alex-berliner/mega_blastoise/cad/renders/nintendo-faceplate.png

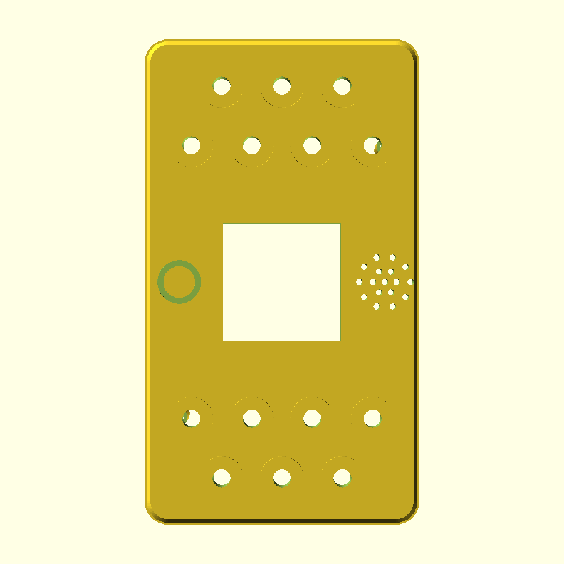
cad/renders/nintendo-faceplate.png
