alex-berliner/mega_blastoise/cad/renders/st7789-nfc-faceplate.png

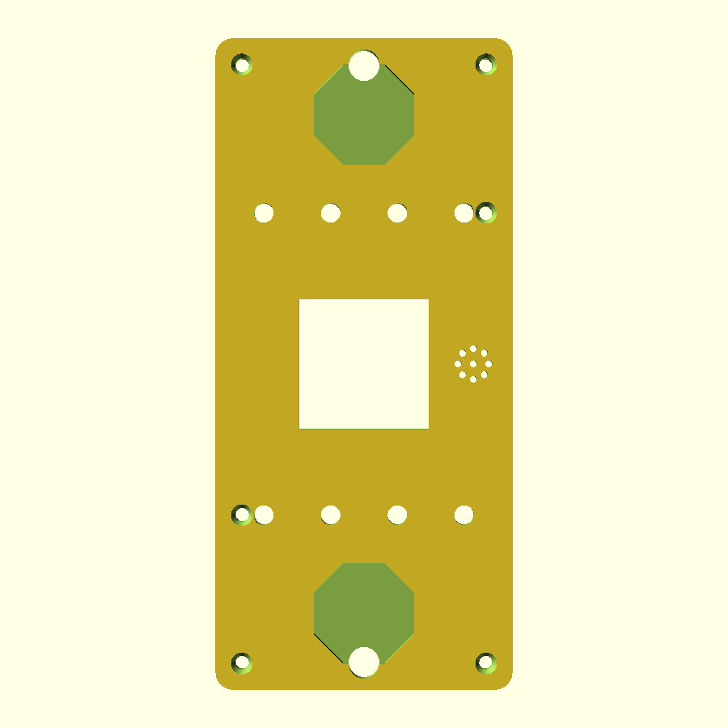
cad/renders/st7789-nfc-faceplate.png
