alex-berliner/mega_blastoise/cad/renders/variants-comparison.png

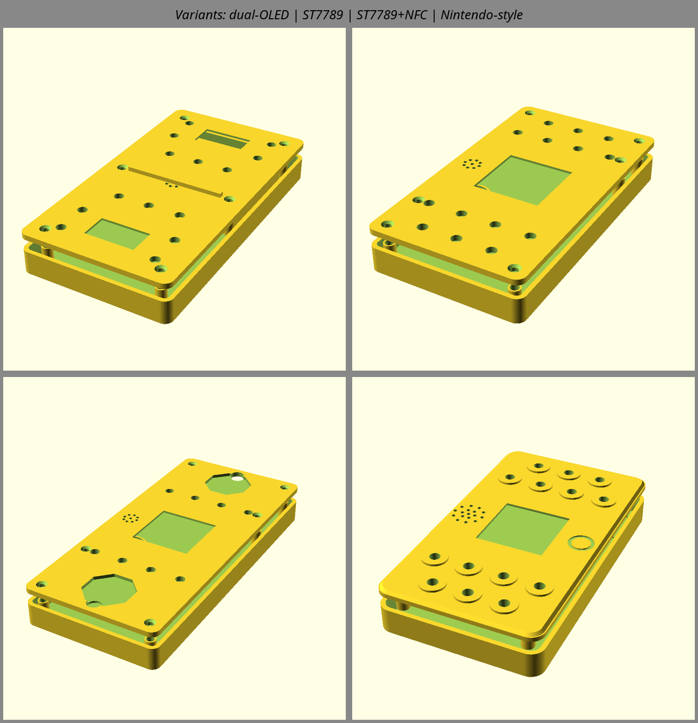
cad/renders/variants-comparison.png
