alex-berliner/mega_blastoise/mega_blastoise_fw/docs/fw_battle_turn.png

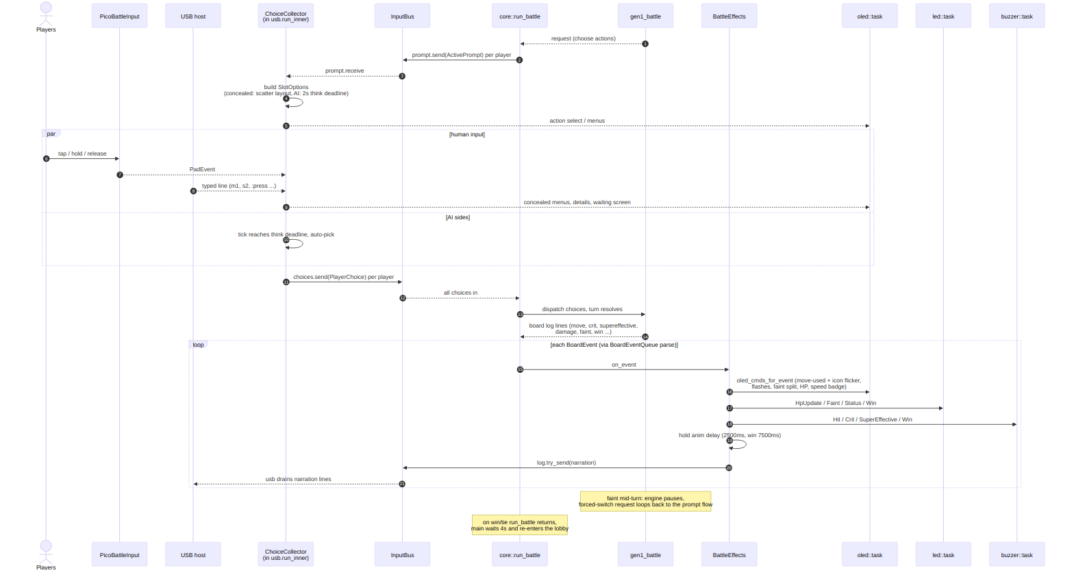
mega_blastoise_fw/docs/fw_battle_turn.png
