alex-berliner/mega_blastoise/mega_blastoise_fw/docs/fw_lobby_sequence.png

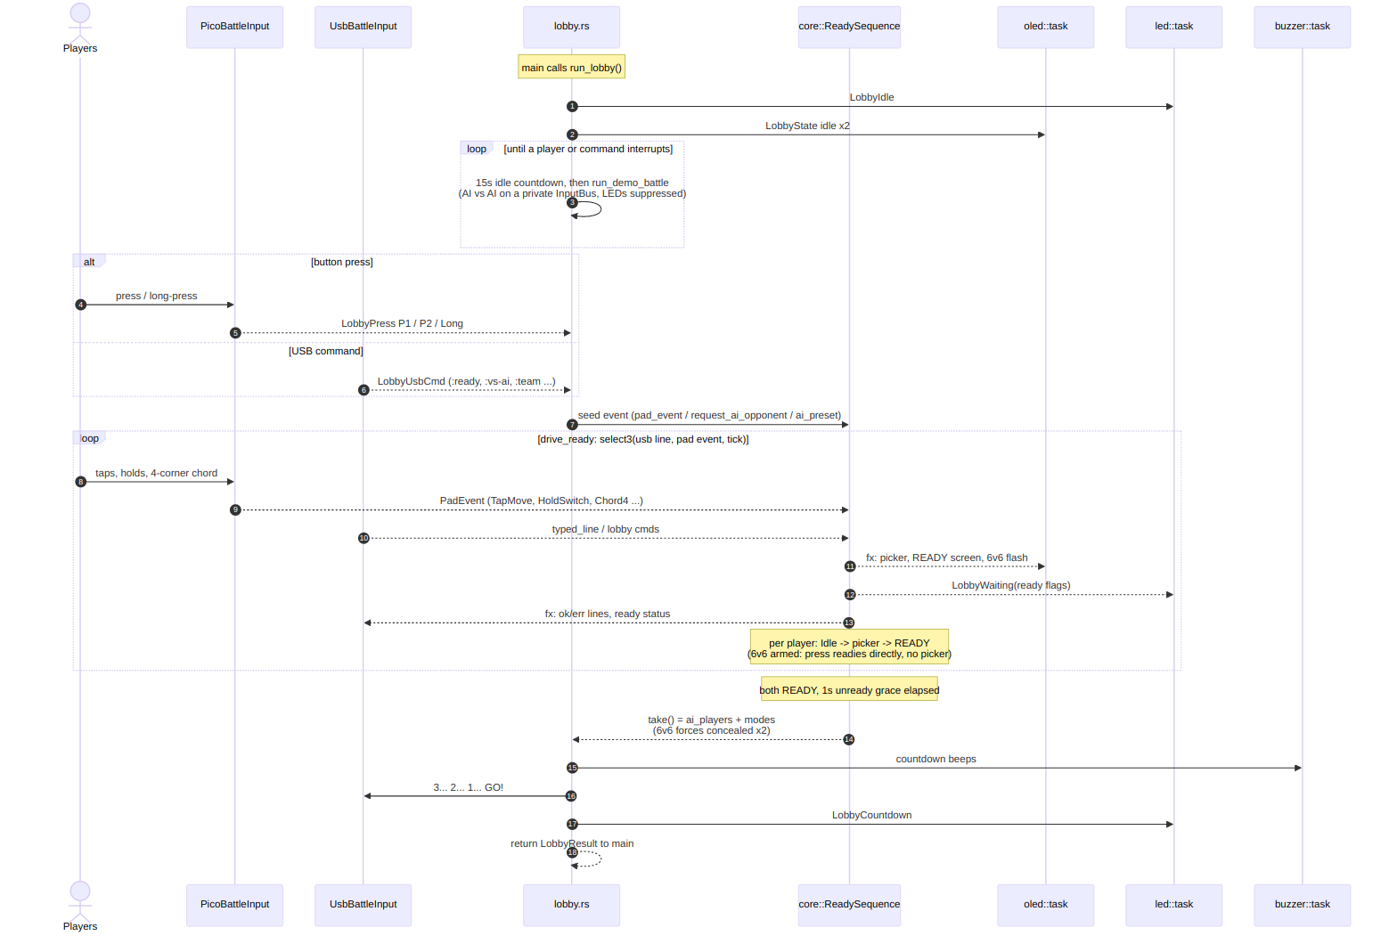
mega_blastoise_fw/docs/fw_lobby_sequence.png
