alex-berliner/mega_blastoise/mega_blastoise_fw/docs/fw_topology.png

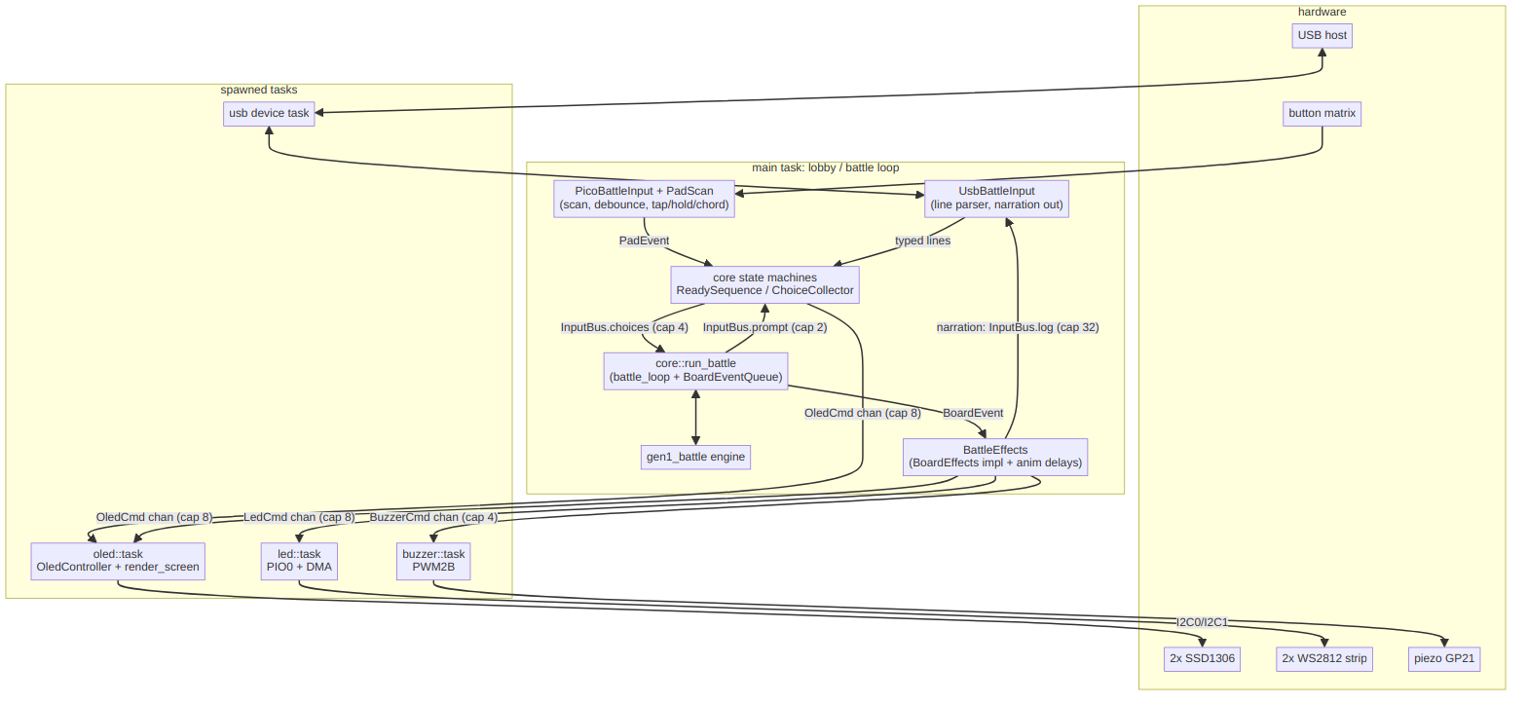
mega_blastoise_fw/docs/fw_topology.png
