alex-berliner/mega_blastoise/cad/renders/assembly-hero.png

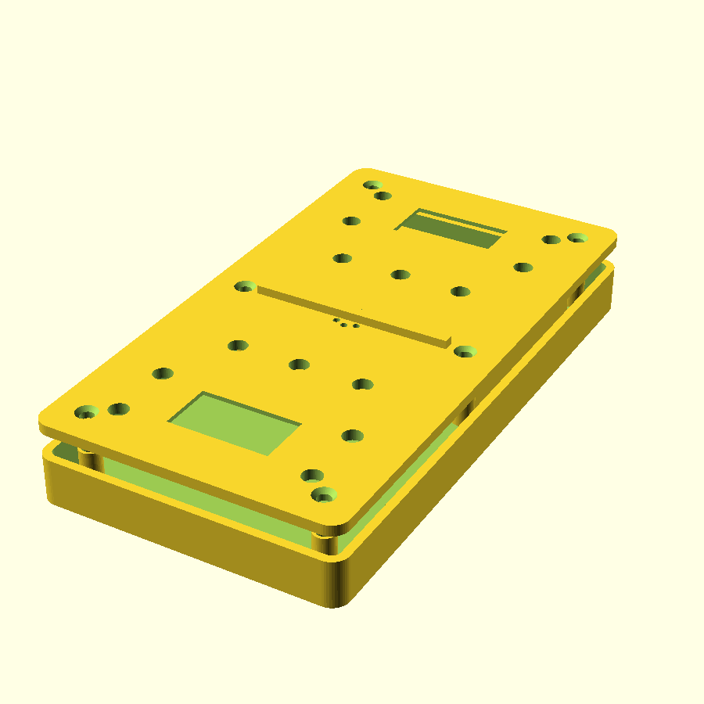
cad/renders/assembly-hero.png
