alex-berliner/mega_blastoise/cad/renders/nintendo-assembly.png

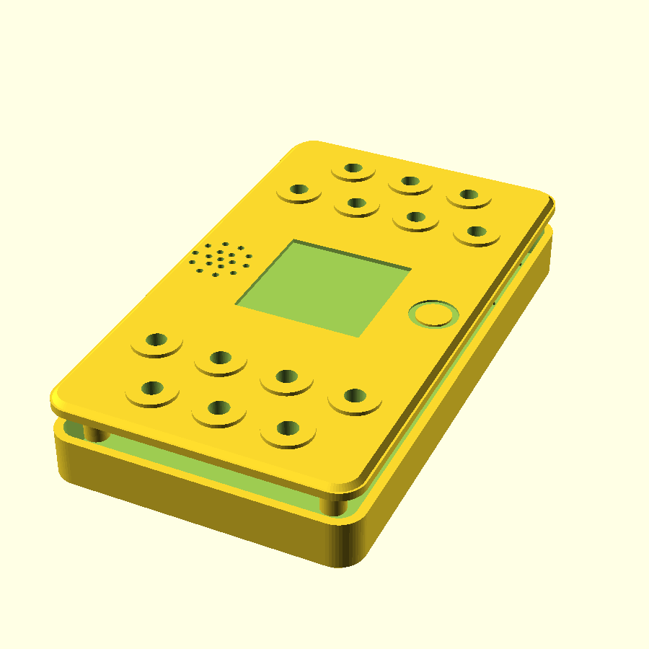
cad/renders/nintendo-assembly.png
