alex-berliner/mega_blastoise/cad/renders/st7789-assembly.png

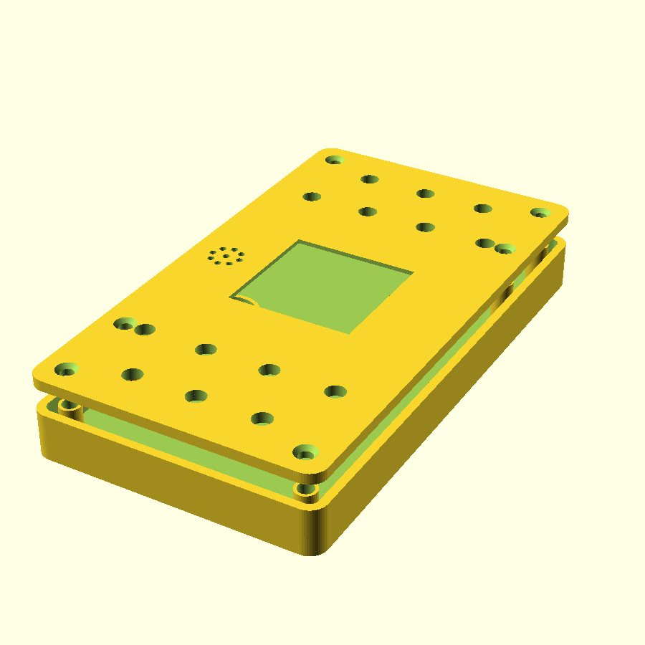
cad/renders/st7789-assembly.png
