alex-berliner/mega_blastoise/cad/renders/st7789-nfc-assembly.png

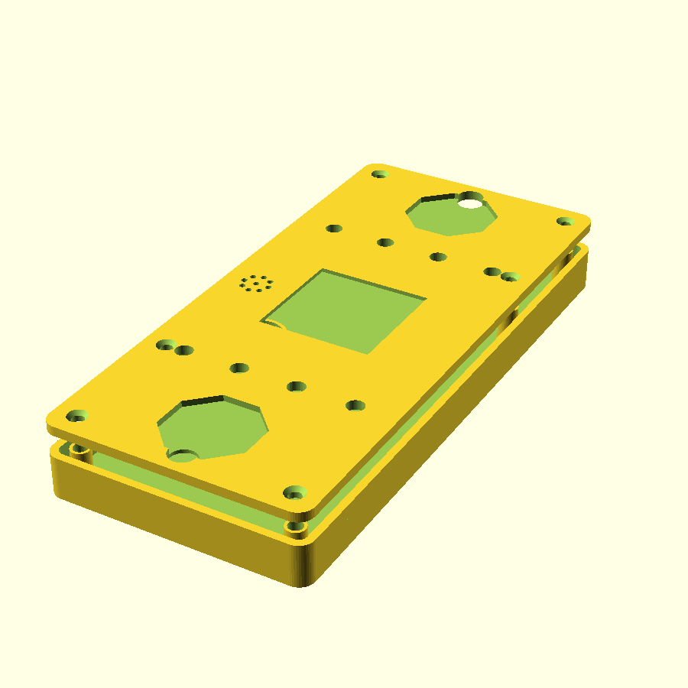
cad/renders/st7789-nfc-assembly.png
