alex-berliner/mega_blastoise/mega_blastoise_core/src/runner/gen1.rs

//! Drives a [`gen1_battle`] battle and narrates it as [`BoardEvent`]s.
//!
//! This is the Gen 1 half of the engine seam; the Gen 3 half is
//! [`crate::runner::gen3`]. Picking a ruleset picks which of the two a
//! caller drives — nothing below the [`InputBus`] knows which ran.
//!
//! The shape differs from Gen 3's because the engines differ: the battler
//! hands out `Request`s and takes choice strings back, so this runner pumps
//! that protocol, while Gen 3 steps a whole turn at once. What they share is
//! everything past the bus — both distil their seats into the neutral
//! [`crate::choice_collect::SlotOptions`], and a player cannot tell from the
//! choosing experience which engine is underneath.

extern crate alloc;

use alloc::string::ToString;

use gen1_battle::{
    BattleType, CoreBattleEngineOptions, CoreBattleOptions, FormatData, PlayerData, PlayerDex,
    PlayerOptions, PlayerType, Request, SerializedRuleSet, SideData, TeamData,
};
use battler_data::DataStore;

use core::future::Future;

use embassy_futures::select::{select, Either};

use crate::battle_effects::{BoardEffects, BoardEventQueue};
use crate::battle_input::{ActivePrompt, InputBus};
use crate::board_event::{board_prompt_event, BoardEvent, MoveSlot};

pub fn make_player(id: &str, name: &str) -> PlayerData {
    PlayerData {
        id: id.to_string(),
        name: name.to_string(),
        player_type: PlayerType::Trainer,
        player_options: PlayerOptions::default(),
        team: TeamData::default(),
        dex: PlayerDex::default(),
    }
}

pub fn battle_options_with_seed(seed: u64) -> CoreBattleOptions {
    CoreBattleOptions {
        seed: Some(seed),
        format: FormatData {
            battle_type: BattleType::Singles,
            rules: SerializedRuleSet::new(),
        },
        field: Default::default(),
        side_1: SideData {
            name: "White".to_string(),
            players: alloc::vec![make_player("p1", "White")],
        },
        side_2: SideData {
            name: "Red".to_string(),
            players: alloc::vec![make_player("p2", "Red")],
        },
    }
}

/// Idle delay (ms) at lobby start before the demo battle begins automatically.
pub const LOBBY_DEMO_DELAY_MS: u64 = 15_000;

pub fn demo_battle_options() -> CoreBattleOptions {
    CoreBattleOptions {
        seed: Some(12345),
        format: FormatData {
            battle_type: BattleType::Singles,
            rules: SerializedRuleSet::new(),
        },
        field: Default::default(),
        side_1: SideData {
            name: "White".to_string(),
            players: alloc::vec![make_player("p1", "White")],
        },
        side_2: SideData {
            name: "Red".to_string(),
            players: alloc::vec![make_player("p2", "Red")],
        },
    }
}

pub fn demo_engine_opts() -> CoreBattleEngineOptions {
    CoreBattleEngineOptions {
        validate_teams: false,
        auto_continue: true,
        reveal_actual_health: true,
        log_time: false,
        ..Default::default()
    }
}

// ── Move slot cache ───────────────────────────────────────────────────────────

// Caches per-player MoveSlot lists for the active Pokémon.  Populated once on
// SwitchIn (full CBOR decode via query_active_moves).  On subsequent Move
// events we only refresh PP from battle RAM — no CBOR decode.
struct MoveSlotCache {
    entries: alloc::vec::Vec<(alloc::string::String, alloc::vec::Vec<MoveSlot>)>,
}

impl MoveSlotCache {
    fn new() -> Self {
        Self { entries: alloc::vec::Vec::new() }
    }

    fn store(&mut self, player_id: &str, slots: alloc::vec::Vec<MoveSlot>) {
        if let Some(e) = self.entries.iter_mut().find(|(id, _)| id == player_id) {
            e.1 = slots;
        } else {
            self.entries.push((player_id.to_string(), slots));
        }
    }

    // Read current PP from battle state (no CBOR, no full PlayerBattleData), update
    // cached slots, return a clone.  Returns empty vec on cache miss.
    fn refresh_pp(
        &mut self,
        player_id: &str,
        battle: &gen1_battle::PublicCoreBattle<'_>,
    ) -> alloc::vec::Vec<MoveSlot> {
        let pp_list = battle.active_mon_move_pp(player_id).unwrap_or_default();

        let Some(entry) = self.entries.iter_mut().find(|(id, _)| id == player_id) else {
            return alloc::vec::Vec::new();
        };
        for (slot, (pp, max_pp)) in entry.1.iter_mut().zip(pp_list.iter()) {
            slot.pp = *pp;
            slot.max_pp = *max_pp;
        }
        entry.1.clone()
    }
}

// ── DataStore lookup (full CBOR decode, called only on SwitchIn) ──────────────

/// Returns (move slots, team slot index) for the currently active mon.
fn query_active_moves<DS: DataStore>(
    battle: &mut gen1_battle::PublicCoreBattle<'_>,
    data: &DS,
    player_id: &str,
) -> (alloc::vec::Vec<MoveSlot>, Option<u8>, Option<u16>) {
    let Ok(player_data) = battle.player_data(player_id) else {
        return (alloc::vec::Vec::new(), None, None);
    };
    let Some((slot_idx, active_mon)) = player_data.mons.into_iter().enumerate().find(|(_, m)| m.active) else {
        return (alloc::vec::Vec::new(), None, None);
    };
    let speed = active_mon.stats.get(&gen1_battle::Stat::Spe).copied();
    let _ = data;
    let moves = active_mon
        .moves
        .into_iter()
        .map(|mv| {
            let info = gen1_battle::move_by_id(&mv.id);
            let (power, accuracy, category) = match info {
                Some(m) => (
                    if m.power > 0 { Some(m.power as u32) } else { None },
                    if m.accuracy > 0 { Some(m.accuracy) } else { None },
                    alloc::format!("{:?}", m.category),
                ),
                None => (None, None, alloc::string::String::from("?")),
            };
            MoveSlot {
                name: mv.name,
                type_name: mv.typ.clone(),
                category,
                power,
                accuracy,
                pp: mv.pp,
                max_pp: mv.max_pp,
            }
        })
        .collect();
    (moves, Some(slot_idx as u8), speed)
}

fn query_team_slot_by_name(battle: &mut gen1_battle::PublicCoreBattle<'_>, player_id: &str, name: &str) -> Option<u8> {
    let data = battle.player_data(player_id).ok()?;
    data.mons.iter().position(|m| m.summary.name.as_str() == name).map(|i| i as u8)
}

// ── Event enrichment ──────────────────────────────────────────────────────────

async fn enrich_and_dispatch<E, DS>(
    battle: &mut gen1_battle::PublicCoreBattle<'_>,
    data: &DS,
    queue: &mut BoardEventQueue,
    effects: &mut E,
    cache: &mut MoveSlotCache,
) where
    E: BoardEffects,
    DS: DataStore,
{
    #[cfg(feature = "timing")]
    let t_drain = embassy_time::Instant::now();

    let entries: alloc::vec::Vec<alloc::string::String> =
        battle.new_log_entries().map(alloc::string::String::from).collect();
    let n_entries = entries.len();
    #[cfg(not(feature = "timing"))]
    let _ = n_entries;

    #[cfg(feature = "timing")]
    let drain_ms = t_drain.elapsed().as_millis();

    #[cfg(feature = "timing")]
    let t_parse = embassy_time::Instant::now();

    queue.push_log_lines(entries.iter().map(alloc::string::String::as_str));

    #[cfg(feature = "timing")]
    let parse_ms = t_parse.elapsed().as_millis();

    #[cfg(feature = "timing")]
    let t_enrich = embassy_time::Instant::now();

    let raw = queue.drain_pending();
    for event in raw {
        let inject = match &event {
            BoardEvent::Move { player_id: Some(pid), .. } => {
                // PP-only refresh from battle RAM — no CBOR decode.
                #[cfg(feature = "timing")]
                let t_pp = embassy_time::Instant::now();

                let moves = cache.refresh_pp(pid.as_str(), battle);

                #[cfg(feature = "timing")]
                defmt::info!("  refresh_pp({}): {}ms", pid.as_str(), t_pp.elapsed().as_millis());

                if moves.is_empty() {
                    // Cache miss (shouldn't happen after SwitchIn) — fall back.
                    #[cfg(feature = "timing")]
                    defmt::info!("  refresh_pp cache miss for {}, falling back", pid.as_str());
                    let (moves, _, _) = query_active_moves(battle, data, pid.as_str());
                    cache.store(pid.as_str(), moves.clone());
                    Some((pid.clone(), moves))
                } else {
                    Some((pid.clone(), moves))
                }
            }
            _ => None,
        };

        let mut inject_extra: Option<(alloc::string::String, alloc::vec::Vec<MoveSlot>)> = None;
        let enriched = match event {
            BoardEvent::SwitchIn { name, species, player_id, moves, .. } if moves.is_empty() => {
                // Full CBOR decode — only happens once per switch-in.
                let (new_moves, slot, speed) = player_id.as_deref().map(|pid| {
                    #[cfg(feature = "timing")]
                    let t_qam = embassy_time::Instant::now();

                    let (moves, slot, speed) = query_active_moves(battle, data, pid);
                    cache.store(pid, moves.clone());

                    #[cfg(feature = "timing")]
                    defmt::info!("  query_active_moves(SwitchIn {}): {}ms", pid, t_qam.elapsed().as_millis());

                    (moves, slot, speed)
                }).unwrap_or((alloc::vec::Vec::new(), None, None));
                BoardEvent::SwitchIn { name, species, player_id, team_slot: slot, moves: new_moves, speed }
            }
            BoardEvent::SwitchIn { name, species, player_id, moves, team_slot, speed } => {
                // Pre-populated — cache for future PP refreshes.
                if let Some(pid) = &player_id {
                    cache.store(pid.as_str(), moves.clone());
                }
                BoardEvent::SwitchIn { name, species, player_id, moves, team_slot, speed }
            }
            BoardEvent::Faint { mon, .. } => {
                let name = mon.split(',').next().unwrap_or(mon.as_str());
                let pid = mon.split(',').nth(1).unwrap_or("");
                let slot = if !pid.is_empty() { query_team_slot_by_name(battle, pid, name) } else { None };
                BoardEvent::Faint { mon, team_slot: slot }
            }
            BoardEvent::EffectStart { ref mon, ref what, .. }
                if what == "transform" || what == "mimic" =>
            {
                // The mon's move NAMES changed — the PP-only cache refresh
                // can't see that. Full re-query, refresh the cache, and
                // update the move corners.
                let pid = mon.split(',').nth(1).unwrap_or("").to_string();
                if !pid.is_empty() {
                    let (moves, _, _) = query_active_moves(battle, data, &pid);
                    cache.store(&pid, moves.clone());
                    if !moves.is_empty() {
                        inject_extra = Some((pid, moves));
                    }
                }
                event
            }
            other => other,
        };

        queue.push_event(enriched);
        if let Some((pid, moves)) = inject_extra {
            queue.push_event(BoardEvent::MovesUpdate { player_id: pid, moves });
        }
        if let Some((pid, moves)) = inject {
            queue.push_event(BoardEvent::MovesUpdate { player_id: pid, moves });
        }
    }

    #[cfg(feature = "timing")]
    let enrich_ms = t_enrich.elapsed().as_millis();

    #[cfg(feature = "timing")]
    let t_dispatch = embassy_time::Instant::now();

    queue.dispatch_all(effects).await;

    #[cfg(feature = "timing")]
    let dispatch_ms = t_dispatch.elapsed().as_millis();

    #[cfg(feature = "timing")]
    if n_entries > 0 || drain_ms + parse_ms + enrich_ms + dispatch_ms > 0 {
        defmt::info!(
            "enrich_and_dispatch: entries={} drain={}ms parse={}ms enrich={}ms dispatch={}ms",
            n_entries as u32,
            drain_ms,
            parse_ms,
            enrich_ms,
            dispatch_ms,
        );
    }
}

// ── Prompt distilling ─────────────────────────────────────────────────────────

/// Distil a Gen 1 battler request into the generation-neutral
/// [`SlotOptions`] the shared collector consumes. This is battle logic — it
/// knows the battler's `Request` shapes — which is why it lives here with the
/// Gen 1 runner and not in `choice_collect`, which must stay engine-blind.
pub fn slot_options_from_request(
    player_id: &str,
    request: &Request,
    player_data: Option<&gen1_battle::PlayerBattleData>,
) -> crate::choice_collect::SlotOptions {
    use crate::battle_input::format_move_choice;
    use crate::choice_collect::SlotOptions;
    use alloc::string::String;

    let mut s = SlotOptions::blank(
        crate::board_event::player_id_to_num(player_id),
        player_id.to_string(),
    );
    if let Some(pd) = player_data {
        for (i, ok) in s.party_ok.iter_mut().enumerate() {
            *ok = pd.mons.get(i).is_some_and(|m| !m.active && m.hp > 0);
        }
        s.party = pd.mons.iter().map(crate::display::party_slot_from_mon).collect();
    }
    match request {
        Request::Turn(turn) => {
            if let Some(mon) = turn.active.first() {
                s.active_slot = Some(mon.team_position as usize);
                let n = mon.moves.len().min(4);
                if n == 0 {
                    s.auto = Some(String::from("pass"));
                } else if mon.locked_into_move {
                    s.auto = Some(format_move_choice(0));
                } else {
                    s.n_moves = n;
                    for i in 0..n {
                        s.usable[i] = !mon.moves[i].disabled && mon.moves[i].pp > 0;
                    }
                    s.trapped = mon.trapped;
                }
            }
        }
        Request::Switch(_) => {
            s.forced_switch = true;
            // A bench of one is still the player's to send out. This used to
            // auto-commit, on the reasoning that a choice with one option is
            // not a choice — but the player is watching their last Pokemon
            // come out, and having the game make that press for them reads
            // as a dropped input rather than a courtesy. The engine
            // validates either way.
        }
        Request::TeamPreview(_) => s.auto = Some(String::from("random")),
        Request::LearnMove(_) => s.auto = Some(String::from("pass")),
    }
    s.prompt_text =
        crate::prompt_fmt::format_prompt(s.player_id.as_str(), request, player_data);
    s
}

// ── Battle runner ─────────────────────────────────────────────────────────────

pub async fn run_battle<E, T, F, DS>(
    battle: &mut gen1_battle::PublicCoreBattle<'_>,
    data: &DS,
    bus: &InputBus,
    inputs: F,
    queue: &mut BoardEventQueue,
    effects: &mut E,
    on_turn: T,
) where
    E: BoardEffects,
    T: FnMut(&mut gen1_battle::PublicCoreBattle<'_>),
    F: Future<Output = ()>,
    DS: DataStore,
{
    match select(battle_loop(battle, data, bus, queue, effects, on_turn), inputs).await {
        Either::First(()) | Either::Second(()) => {}
    }
}

async fn battle_loop<E, T, DS>(
    battle: &mut gen1_battle::PublicCoreBattle<'_>,
    data: &DS,
    bus: &InputBus,
    queue: &mut BoardEventQueue,
    effects: &mut E,
    mut on_turn: T,
) where
    E: BoardEffects,
    T: FnMut(&mut gen1_battle::PublicCoreBattle<'_>),
    DS: DataStore,
{
    let mut cache = MoveSlotCache::new();
    #[cfg(feature = "trace")]
    defmt::info!("[trace] battle_loop: start, initial dispatch");
    enrich_and_dispatch(battle, data, queue, effects, &mut cache).await;

    // The turn counter feeds only the trace logs.
    #[cfg(feature = "trace")]
    let mut turn: u32 = 0;
    while !battle.ended() {
        #[cfg(feature = "trace")]
        {
            turn += 1;
        }
        #[cfg(feature = "trace")]
        defmt::info!("[trace] battle_loop: turn {}", turn);
        let mut had_request = false;
        loop {
            // Collect ALL active requests before sending any prompts, so both
            // players are prompted simultaneously and can inspect their screens
            // in parallel without waiting on each other.
            let requests: alloc::vec::Vec<(alloc::string::String, Request)> = battle
                .active_requests()
                .map(|(pid, req)| (pid.to_string(), req.clone()))
                .collect();

            if requests.is_empty() { break; }
            had_request = true;

            #[cfg(feature = "trace")]
            defmt::info!("[trace] battle_loop: {} request(s) this turn", requests.len() as u32);

            // Send all prompts to bus.prompt before collecting any choices.
            let batch_total = requests.len();
            for (player_id, request) in &requests {
                #[cfg(feature = "trace")]
                defmt::info!("[trace] battle_loop: sending prompt to {}", player_id.as_str());
                // Refresh the OLED move corners for this prompt. Normally a
                // PP refresh from battle RAM; a recharging mon instead shows
                // its synthetic single "Recharge" option.
                if let Request::Turn(turn) = request {
                    let is_recharge = turn
                        .active
                        .first()
                        .is_some_and(|a| a.moves.len() == 1 && a.moves[0].id == "recharge");
                    let moves = if is_recharge {
                        alloc::vec![MoveSlot {
                            name: alloc::string::String::from("Recharge"),
                            type_name: alloc::string::String::from("Normal"),
                            category: alloc::string::String::from("Status"),
                            power: None,
                            accuracy: None,
                            pp: 1,
                            max_pp: 1,
                        }]
                    } else {
                        cache.refresh_pp(player_id, battle)
                    };
                    if !moves.is_empty() {
                        queue.push_event(BoardEvent::MovesUpdate {
                            player_id: player_id.clone(),
                            moves,
                        });
                    }
                }
                queue.push_event(board_prompt_event(player_id, request));
                queue.dispatch_all(effects).await;
                let player_data = battle.player_data(player_id).ok();
                let slot =
                    slot_options_from_request(player_id, request, player_data.as_ref());
                bus.prompt.send(ActivePrompt {
                    player_id: player_id.clone(),
                    slot,
                    batch_total,
                }).await;
                #[cfg(feature = "trace")]
                defmt::info!("[trace] battle_loop: prompt delivered to {}", player_id.as_str());
            }

            // Collect one choice per prompted player, routed by the id tag so
            // sources may submit in any order.
            let mut pending: alloc::vec::Vec<&str> =
                requests.iter().map(|(pid, _)| pid.as_str()).collect();
            while !pending.is_empty() {
                #[cfg(feature = "trace")]
                defmt::info!("[trace] battle_loop: waiting for {} choice(s)", pending.len() as u32);
                let submitted = bus.choices.receive().await;
                let Some(pos) = pending.iter().position(|pid| *pid == submitted.player_id) else {
                    // Duplicate or stray submission — this turn already has that
                    // player's choice (or the player has no request). Drop it.
                    #[cfg(feature = "defmt")]
                    defmt::error!(
                        "battle_loop: dropping choice for {} with no pending request",
                        submitted.player_id.as_str()
                    );
                    continue;
                };
                let player_id = pending.remove(pos);
                let line = submitted.choice;
                #[cfg(feature = "trace")]
                defmt::info!("[trace] battle_loop: got choice from {}: {}", player_id, line.as_str());

                #[cfg(feature = "timing")]
                let t0 = embassy_time::Instant::now();

                if let Err(e) = battle.set_player_choice(player_id, &line) {
                    #[cfg(feature = "defmt")]
                    defmt::error!(
                        "set_player_choice failed ({}): {}",
                        player_id,
                        defmt::Display2Format(&e.to_string())
                    );
                    #[cfg(not(feature = "defmt"))]
                    let _ = e;
                }

                #[cfg(feature = "timing")]
                defmt::info!(
                    "set_player_choice({}): {}ms",
                    player_id,
                    t0.elapsed().as_millis()
                );

                #[cfg(feature = "timing")]
                let t_ead = embassy_time::Instant::now();

                enrich_and_dispatch(battle, data, queue, effects, &mut cache).await;

                #[cfg(feature = "timing")]
                defmt::info!(
                    "enrich_and_dispatch after set_player_choice({}): {}ms",
                    player_id,
                    t_ead.elapsed().as_millis()
                );
            }
        }

        if !had_request {
            enrich_and_dispatch(battle, data, queue, effects, &mut cache).await;
            continue;
        }

        enrich_and_dispatch(battle, data, queue, effects, &mut cache).await;
        on_turn(battle);
    }
    #[cfg(feature = "trace")]
    defmt::info!("[trace] battle_loop: ended after {} turn(s)", turn);
}
