alex-berliner/mega_blastoise/mega_blastoise_web/src/lib.rs

mod web_display;
mod web_effects;

use std::cell::RefCell;
use std::collections::VecDeque;
use std::future::Future;
use std::pin::Pin;
use std::task::{Context, Poll, Waker};

use gen1_battle::TeamData;
use js_sys::Date;
use wasm_bindgen::prelude::*;
use wasm_bindgen_futures::spawn_local;

use embassy_futures::select::{select, select3, Either, Either3};
use mega_blastoise_core::{
    battle_options_with_seed, demo_engine_opts, draw_two_randbat_teams, format_active_state,
    render_screen, run_battle, ActivePrompt, BoardEventQueue,
    ChoiceCollector, CollectEffect, ControlMode, FlashDataStore, InputBus,
    OledCmd, OledController, PadEvent, PartySlotData, PlayerChoice,
    RandomAi, ReadySequence, SlotOptions,
    BATTLE_HELP, COLLECT_TICK_MS, LOBBY_DEMO_DELAY_MS,
};
use gen3_battle::Ruleset;
use mega_blastoise_core::device_session::{Button, Ctx, DeviceSession, Out};
use mega_blastoise_core::device_ui;
use web_effects::WebBattleEffects;
use web_display::WasmDisplay;

// ── Global state ──────────────────────────────────────────────────────────────

thread_local! {
    static P1_PIXELS: RefCell<Vec<u8>> = RefCell::new(vec![10, 25, 10, 255].repeat(128 * 64));
    static P2_PIXELS: RefCell<Vec<u8>> = RefCell::new(vec![10, 25, 10, 255].repeat(128 * 64));
    static LED_STATE: RefCell<[u32; 24]> = RefCell::new([0u32; 24]);

    // The single-screen device outside a battle turn: menus, options,
    // per-seat cursors and overlays, the log, and what a button means.
    // ALL of it lives in core (the fidelity rule); this cell is only where
    // the web keeps the one instance.
    static SESSION: RefCell<DeviceSession> = RefCell::new(DeviceSession::new());

    // Per-player button queues — both players can pre-queue independently
    static P1_QUEUE: RefCell<VecDeque<ButtonEvent>> = RefCell::new(VecDeque::new());
    static P1_WAKER: RefCell<Option<Waker>> = RefCell::new(None);
    static P2_QUEUE: RefCell<VecDeque<ButtonEvent>> = RefCell::new(VecDeque::new());
    static P2_WAKER: RefCell<Option<Waker>> = RefCell::new(None);

    // Battle-input queue: classified pad events and typed lines, consumed by
    // the shared ChoiceCollector loop (mirrors the firmware's USB+matrix IO).
    static BATTLE_INPUT: RefCell<VecDeque<BattleInput>> = RefCell::new(VecDeque::new());
    static BATTLE_INPUT_WAKER: RefCell<Option<Waker>> = RefCell::new(None);

    // Sticky holds (web only): a PC mouse can't hold one button while
    // clicking another, so a hold LATCHES — it stays "held down" until the
    // button is clicked again or the player commits an option. Entries are
    // (is_switch, idx), innermost last; releases are swallowed while latched.
    static HELD_LATCH: RefCell<[Vec<(bool, u8)>; 2]> = RefCell::new([Vec::new(), Vec::new()]);

    // Unlatching an OUTER button while an inner one is still latched defers
    // its HoldEnd until the inner unlatches (the screen must stay on the
    // inner view until then).
    static PENDING_END: RefCell<[u8; 2]> = RefCell::new([0; 2]);

    // Control scheme each player chose this battle (drives the web-only
    // "action buttons open instantly on click" behavior for Concealed).
    static CONTROL_MODES: RefCell<[ControlMode; 2]> = RefCell::new([ControlMode::Normal; 2]);


    // Lobby LED animation mode
    static LOBBY_MODE: RefCell<bool> = RefCell::new(false);


    // Flash events: [p1_type, p2_type]; 1 = super-effective, 2 = crit; consumed on read
    static FLASH: RefCell<[u8; 2]> = RefCell::new([0, 0]);

    // The shared two-display state machine (mega_blastoise_core::oled_ctl) —
    // identical to the firmware's. All screen decisions happen in here;
    // this file only repaints canvases when it says so. See oled_apply().
    static OLED_CTL: RefCell<OledController> = RefCell::new(OledController::new());

    // Full party snapshot per player (for AI switch picks + party LED sync;
    // the OLED controller keeps its own copy via OledCmd::PartyUpdate)
    static P1_PARTY: RefCell<Vec<PartySlotData>> = RefCell::new(Vec::new());
    static P2_PARTY: RefCell<Vec<PartySlotData>> = RefCell::new(Vec::new());

    // Which players are AI-controlled this game (reset each lobby)
    static AI_PLAYERS: RefCell<[bool; 2]> = RefCell::new([false, false]);

    // Demo mode: both AI, auto-restart each game (persists until page reload)
    static DEMO_MODE: RefCell<bool> = RefCell::new(false);

    // AI pause: when true, AI players block in wait_action/wait_switch
    static AI_PAUSED: RefCell<bool> = RefCell::new(false);

    // Pending AI config for the next game: set by VS AI button, survives the
    // loop-top reset of AI_PLAYERS, applied just before the battle starts.
    static NEXT_GAME_AI: RefCell<Option<[bool; 2]>> = RefCell::new(None);

    // When false, all animation sleeps are skipped (useful for CLI testing).
    static ANIM_ENABLED: RefCell<bool> = RefCell::new(true);

    // A button press during battle dialog skips the current animation delay
    // (consumed at the start of each delay so stale presses don't skip).
    static SKIP_DIALOG: RefCell<[bool; 2]> = RefCell::new([false, false]);

    // Screen tracer: the last [p1, p2, view] labels, so a state change logs
    // once instead of once per frame.
    static LAST_SCREEN_STATE: RefCell<[String; 3]> =
        RefCell::new([String::new(), String::new(), String::new()]);

}

// ── State accessors (pub(crate)) ──────────────────────────────────────────────

/// Apply a display command to the shared controller and repaint whichever
/// canvases it changed. The ONLY write path to the OLED canvases — mirrors
/// the firmware's OLED task loop (apply → render `ctl.screen(p)` → flush).
pub(crate) fn oled_apply(cmd: OledCmd) {
    let redraw = OLED_CTL.with(|c| c.borrow_mut().apply(cmd));
    for player in [1u8, 2] {
        if redraw.includes(player) {
            let mut disp = WasmDisplay::new();
            OLED_CTL.with(|c| render_screen(&mut disp, &c.borrow().screen(player)));
            let pixels = disp.to_rgba();
            if player == 1 { P1_PIXELS.with(|p| *p.borrow_mut() = pixels); }
            else           { P2_PIXELS.with(|p| *p.borrow_mut() = pixels); }
        }
    }
}

/// Advance the battle-screen sprite bobs — called every BOB_TICK_MS from JS,
/// mirroring the firmware's OLED-task tick. Each player's bob rate scales
/// with their active mon's Speed stat.
#[wasm_bindgen]
pub fn wasm_tick_bob() {
    let redraw = OLED_CTL.with(|c| c.borrow_mut().tick_bob(mega_blastoise_core::BOB_TICK_MS));
    for player in [1u8, 2] {
        if redraw.includes(player) {
            let mut disp = WasmDisplay::new();
            OLED_CTL.with(|c| render_screen(&mut disp, &c.borrow().screen(player)));
            let pixels = disp.to_rgba();
            if player == 1 { P1_PIXELS.with(|p| *p.borrow_mut() = pixels); }
            else           { P2_PIXELS.with(|p| *p.borrow_mut() = pixels); }
        }
    }
}

pub(crate) fn is_ai_paused() -> bool {
    AI_PAUSED.with(|p| *p.borrow())
}

pub(crate) fn is_ai_player(player: u8) -> bool {
    AI_PLAYERS.with(|a| a.borrow()[(player - 1) as usize])
}





pub(crate) fn clear_input_queues() {
    P1_QUEUE.with(|q| q.borrow_mut().clear());
    P2_QUEUE.with(|q| q.borrow_mut().clear());
}




pub(crate) fn update_leds(leds: [u32; 24]) {
    LED_STATE.with(|l| *l.borrow_mut() = leds);
}

fn status_led_color(status: Option<&str>) -> u32 {
    fn rgb(r: u8, g: u8, b: u8) -> u32 { ((r as u32) << 16) | ((g as u32) << 8) | b as u32 }
    match status {
        None | Some("") => rgb(0,   160, 0),
        Some("par")     => rgb(220, 180, 0),
        Some("brn")     => rgb(220, 20,  0),
        Some("frz")     => rgb(60,  80,  255),
        Some("psn")     => rgb(180, 60,  220),
        Some("tox")     => rgb(80,  0,   100),
        Some("slp")     => rgb(220, 80,  80),
        _               => rgb(0,   160, 0),
    }
}

/// Update HP bar (indices 0-7) for one player only.
/// Party LEDs (8-10 / 20-22) are managed separately by sync_party_leds.
pub(crate) fn update_hp_leds(player: u8, frame: [u32; 8]) {
    LED_STATE.with(|l| {
        let mut leds = l.borrow_mut();
        let base = if player == 1 { 0 } else { 12 };
        for i in 0..8 { leds[base + i] = frame[i]; }
    });
}

/// Rewrite party LEDs (3 slots per player) from P_PARTY status data.
/// Each slot is colored by status (or green if healthy, off if fainted).
/// The old dedicated status LED position (11/23) is zeroed out.
pub(crate) fn sync_party_leds(player: u8) {
    let party = if player == 1 { P1_PARTY.with(|p| p.borrow().clone()) }
                else           { P2_PARTY.with(|p| p.borrow().clone()) };
    LED_STATE.with(|l| {
        let mut leds = l.borrow_mut();
        let base = if player == 1 { 8 } else { 20 };
        let green = status_led_color(None);
        for i in 0..3usize {
            // P2's board is oriented in reverse, so mirror the slot→LED mapping.
            let party_idx = if player == 2 { 2 - i } else { i };
            leds[base + i] = if party.is_empty() {
                green // party not yet populated — default to all healthy
            } else {
                match party.get(party_idx) {
                    Some(slot) if slot.hp > 0 => status_led_color(slot.status.as_deref()),
                    _ => 0,
                }
            };
        }
        leds[base + 3] = 0; // old status-LED position — always off
    });
}

/// Patch a party slot's status in P_PARTY without a full replace.
/// Call after SetStatus/CureStatus so sync_party_leds sees the new value.
pub(crate) fn update_party_slot_status(player: u8, mon_name: &str, status: Option<String>) {
    if player == 1 {
        P1_PARTY.with(|p| {
            if let Some(slot) = p.borrow_mut().iter_mut().find(|s| s.name == mon_name) {
                slot.status = status;
            }
        });
    } else {
        P2_PARTY.with(|p| {
            if let Some(slot) = p.borrow_mut().iter_mut().find(|s| s.name == mon_name) {
                slot.status = status;
            }
        });
    }
}

/// Patch a party slot's HP in P_PARTY (used on Faint to set hp=0).
pub(crate) fn update_party_slot_hp(player: u8, mon_name: &str, hp: u16) {
    if player == 1 {
        P1_PARTY.with(|p| {
            if let Some(slot) = p.borrow_mut().iter_mut().find(|s| s.name == mon_name) {
                slot.hp = hp;
            }
        });
    } else {
        P2_PARTY.with(|p| {
            if let Some(slot) = p.borrow_mut().iter_mut().find(|s| s.name == mon_name) {
                slot.hp = hp;
            }
        });
    }
}

pub(crate) fn set_lobby_mode(active: bool) {
    LOBBY_MODE.with(|m| *m.borrow_mut() = active);
}

pub(crate) fn pack_rgb(r: u8, g: u8, b: u8) -> u32 {
    ((r as u32) << 16) | ((g as u32) << 8) | (b as u32)
}

/// Sleep unconditionally — the collector tick and countdown clocks must run
/// even with `:anim off` (sleep_ms below is animation-gated).
pub(crate) async fn sleep_ms_raw(ms: u32) {
    let promise = js_sys::Promise::new(&mut |resolve: js_sys::Function, _| {
        web_sys::window()
            .unwrap()
            .set_timeout_with_callback_and_timeout_and_arguments_0(&resolve, ms as i32)
            .unwrap();
    });
    wasm_bindgen_futures::JsFuture::from(promise).await.ok();
}

pub(crate) async fn sleep_ms(ms: u32) {
    if !ANIM_ENABLED.with(|a| *a.borrow()) { return; }
    let promise = js_sys::Promise::new(&mut |resolve: js_sys::Function, _| {
        web_sys::window()
            .unwrap()
            .set_timeout_with_callback_and_timeout_and_arguments_0(&resolve, ms as i32)
            .unwrap();
    });
    wasm_bindgen_futures::JsFuture::from(promise).await.ok();
}

/// `player` wants the current narration to move on. It only does once BOTH
/// seats have asked: a shared screen that either player can skip means one of
/// them reads half a battle. An AI seat is always willing, so a lone human
/// playing the robot still skips at their own pace.
pub(crate) fn request_dialog_skip(player: u8) {
    if (1..=2).contains(&player) {
        SKIP_DIALOG.with(|s| s.borrow_mut()[(player - 1) as usize] = true);
    }
}

fn both_want_to_skip() -> bool {
    SKIP_DIALOG.with(|s| {
        let want = s.borrow();
        (0..2).all(|i| want[i] || is_ai_player(i as u8 + 1))
    })
}

/// Animation-gated sleep that any button press cuts short (mirrors the
/// firmware's DIALOG_SKIP): polls in 50 ms slices, consuming the skip flag
/// at the start so only presses made DURING the dialog skip it.
pub(crate) async fn sleep_ms_skippable(ms: u32) {
    if !ANIM_ENABLED.with(|a| *a.borrow()) { return; }
    SKIP_DIALOG.with(|s| *s.borrow_mut() = [false, false]);
    let mut left = ms;
    while left > 0 {
        let step = left.min(50);
        sleep_ms_raw(step).await;
        if both_want_to_skip() {
            SKIP_DIALOG.with(|s| *s.borrow_mut() = [false, false]);
            return;
        }
        left -= step;
    }
}

pub(crate) fn set_flash(player: u8, flash_type: u8) {
    FLASH.with(|f| f.borrow_mut()[(player - 1) as usize] = flash_type);
}

fn lobby_led_frame() -> [u32; 24] {
    let ready = SESSION.with(|s| s.borrow().lobby_ready());
    let t = (Date::now() as u64 / 30) as u8;
    let v = (if t < 128 { t / 2 } else { (255u8.wrapping_sub(t)) / 2 }) as u32 * 2;
    // Per-player identity colors, mirroring the fw lobby: P1 white, P2 red.
    let breathe_p1 = pack_rgb(v as u8, v as u8, v as u8);
    let breathe_p2 = pack_rgb(v as u8, 0, 0);
    let done = pack_rgb(0, 200, 50);
    let mut frame = [0u32; 24];
    let c1 = if ready[0] { done } else { breathe_p1 };
    let c2 = if ready[1] { done } else { breathe_p2 };
    for i in 0..12  { frame[i] = c1; }
    for i in 12..24 { frame[i] = c2; }
    frame
}

/// `?` / `:help` — same layout as the firmware's device help; the battle
/// section is the shared BATTLE_HELP so the grammars can't drift.
fn print_help() {
    print_log("[help] Web commands");
    print_log("  Lobby:");
    for l in [
        ":ready            both players ready (human)",
        ":ready p1|p2      one player ready (human)",
        ":ready ai         P1 is AI (play as P2; also the RED VS AI button)",
        ":demo             AI vs AI demo (also the DEMO button)",
    ] {
        print_log(&format!("    {l}"));
    }
    print_log("  Any time:");
    for l in [
        ":help / :h / ?    this list",
        ":anim on|off      battle animations",
        ":screens          what each seat is looking at right now",
        ":reset            reload (new battle)",
    ] {
        print_log(&format!("    {l}"));
    }
    print_log("  In battle:");
    for l in BATTLE_HELP {
        print_log(&format!("    {l}"));
    }
}

/// Mirror a diagnostic line into the browser console, where the in-page
/// console panel picks it up. The device UI has no `#log` element, so without
/// this every event line the two-OLED page shows would vanish there.
pub(crate) fn console_log(line: &str) {
    web_sys::console::log_1(&line.into());
}

pub(crate) fn print_log(line: &str) {
    console_log(line);
    let doc = match web_sys::window().and_then(|w| w.document()) {
        Some(d) => d,
        None => return,
    };
    if let Some(el) = doc.get_element_by_id("log") {
        el.insert_adjacent_text("beforeend", &format!("{line}\n")).ok();
        el.set_scroll_top(el.scroll_height());
    }
}

// ── Button events ─────────────────────────────────────────────────────────────

pub enum ButtonEvent {
    Move   { player: u8, slot: u8 },
    Switch { player: u8, idx:  u8 },
    /// Lobby long-press: `player` wants an AI opponent.
    LongPress { player: u8 },
    /// HIDDEN: the 4-corner chord (web: all four corners tapped within 2s).
    Chord { player: u8 },
    /// A demo / VS-AI button set NEXT_GAME_AI; the lobby loop applies it.
    AiPreset,
    /// A typed lobby line for the ready sequence (picker grammar, sims).
    Line(String),
}

// Wait for either player's button (lobby start)
pub(crate) struct AnyButtonFuture;

impl Future for AnyButtonFuture {
    type Output = ButtonEvent;

    fn poll(self: Pin<&mut Self>, cx: &mut Context<'_>) -> Poll<ButtonEvent> {
        let ev = P1_QUEUE.with(|q| q.borrow_mut().pop_front())
            .or_else(|| P2_QUEUE.with(|q| q.borrow_mut().pop_front()));
        if let Some(ev) = ev {
            Poll::Ready(ev)
        } else {
            P1_WAKER.with(|w| *w.borrow_mut() = Some(cx.waker().clone()));
            P2_WAKER.with(|w| *w.borrow_mut() = Some(cx.waker().clone()));
            Poll::Pending
        }
    }
}

// Wait for a specific player's button
pub(crate) struct PlayerButtonFuture(pub u8);

impl Future for PlayerButtonFuture {
    type Output = ButtonEvent;

    fn poll(self: Pin<&mut Self>, cx: &mut Context<'_>) -> Poll<ButtonEvent> {
        let player = self.0;
        let ev = if player == 1 {
            P1_QUEUE.with(|q| q.borrow_mut().pop_front())
        } else {
            P2_QUEUE.with(|q| q.borrow_mut().pop_front())
        };
        if let Some(ev) = ev {
            Poll::Ready(ev)
        } else {
            if player == 1 {
                P1_WAKER.with(|w| *w.borrow_mut() = Some(cx.waker().clone()));
            } else {
                P2_WAKER.with(|w| *w.borrow_mut() = Some(cx.waker().clone()));
            }
            Poll::Pending
        }
    }
}

/// One unit of battle input from the page: a classified pad event or a line
/// typed into the terminal.
enum BattleInput {
    Pad(PadEvent),
    Line(String),
}

fn push_battle_input(inp: BattleInput) {
    BATTLE_INPUT.with(|q| q.borrow_mut().push_back(inp));
    BATTLE_INPUT_WAKER.with(|w| {
        if let Some(waker) = w.borrow_mut().take() {
            waker.wake();
        }
    });
}

/// Resolves with the next battle input (pad event or typed line).
struct BattleInputFuture;

impl Future for BattleInputFuture {
    type Output = BattleInput;

    fn poll(self: Pin<&mut Self>, cx: &mut Context<'_>) -> Poll<BattleInput> {
        if let Some(inp) = BATTLE_INPUT.with(|q| q.borrow_mut().pop_front()) {
            Poll::Ready(inp)
        } else {
            BATTLE_INPUT_WAKER.with(|w| *w.borrow_mut() = Some(cx.waker().clone()));
            Poll::Pending
        }
    }
}

fn push_button(ev: ButtonEvent) {
    let player = match &ev {
        ButtonEvent::Move   { player, .. }
        | ButtonEvent::Switch { player, .. }
        | ButtonEvent::LongPress { player }
        | ButtonEvent::Chord { player } => *player,
        ButtonEvent::AiPreset | ButtonEvent::Line(_) => 1,
    };
    if player == 1 {
        P1_QUEUE.with(|q| q.borrow_mut().push_back(ev));
        P1_WAKER.with(|w| { if let Some(waker) = w.borrow_mut().take() { waker.wake(); } });
    } else {
        P2_QUEUE.with(|q| q.borrow_mut().push_back(ev));
        P2_WAKER.with(|w| { if let Some(waker) = w.borrow_mut().take() { waker.wake(); } });
    }
}

// ── Sticky hold latch (web only) ──────────────────────────────────────────────

fn latch_i(player: u8) -> usize {
    (player.clamp(1, 2) - 1) as usize
}

/// If `(is_switch, idx)` is latched, unlatch it and emit what it owes:
/// the INNERMOST latch emits its HoldEnd immediately (plus any deferred
/// outer ends); an outer latch under a still-latched inner defers its
/// HoldEnd until the inner unlatches, so the inner view stays up.
/// Returns true if the button was latched.
fn unlatch_if_held(player: u8, is_switch: bool, idx: u8) -> bool {
    let i = latch_i(player);
    let (was_latched, ends) = HELD_LATCH.with(|l| {
        let v = &mut l.borrow_mut()[i];
        match v.iter().position(|&e| e == (is_switch, idx)) {
            None => (false, 0u8),
            Some(pos) if pos + 1 == v.len() => {
                v.remove(pos);
                let deferred = PENDING_END.with(|p| core::mem::take(&mut p.borrow_mut()[i]));
                (true, 1 + deferred)
            }
            Some(pos) => {
                v.remove(pos);
                PENDING_END.with(|p| p.borrow_mut()[i] += 1);
                (true, 0)
            }
        }
    });
    for _ in 0..ends {
        push_battle_input(BattleInput::Pad(PadEvent::HoldEnd { player }));
    }
    was_latched
}

fn latch_held(player: u8, is_switch: bool, idx: u8) {
    HELD_LATCH.with(|l| l.borrow_mut()[latch_i(player)].push((is_switch, idx)));
}

fn any_latched(player: u8) -> bool {
    HELD_LATCH.with(|l| !l.borrow()[latch_i(player)].is_empty())
}

pub(crate) fn clear_hold_latch(player: u8) {
    HELD_LATCH.with(|l| l.borrow_mut()[latch_i(player)].clear());
    PENDING_END.with(|p| p.borrow_mut()[latch_i(player)] = 0);
}

pub(crate) fn clear_hold_latches() {
    clear_hold_latch(1);
    clear_hold_latch(2);
}

/// Latched buttons per player, for the page to render as "held" — bit 0-3 =
/// move buttons, bit 4-6 = party buttons.
#[wasm_bindgen]
pub fn wasm_held_buttons(player: u8) -> u8 {
    HELD_LATCH.with(|l| {
        l.borrow()[latch_i(player)]
            .iter()
            .fold(0u8, |m, &(sw, idx)| m | 1 << (if sw { 4 + idx } else { idx }))
    })
}

// ── WASM exports ──────────────────────────────────────────────────────────────

#[wasm_bindgen] pub fn press_move(player: u8, slot: u8) {
    if LOBBY_MODE.with(|m| *m.borrow()) {
        // The hidden 4-corner chord is gone with the corner buttons; 6v6
        // lives in the options menu.
        push_button(ButtonEvent::Move { player, slot });
    } else if unlatch_if_held(player, false, slot) {
        // Clicking a latched button releases the sticky hold.
    } else {
        request_dialog_skip(player);
        push_battle_input(BattleInput::Pad(PadEvent::TapMove { player, slot }));
    }
}

#[wasm_bindgen] pub fn press_switch(player: u8, idx: u8) {
    if LOBBY_MODE.with(|m| *m.borrow()) {
        push_button(ButtonEvent::Switch { player, idx });
    } else if unlatch_if_held(player, true, idx) {
        // Clicking a latched button releases the sticky hold.
    } else {
        // (Concealed menus toggle on plain taps now — no hold conversion.)
        request_dialog_skip(player);
        push_battle_input(BattleInput::Pad(PadEvent::TapSwitch { player, idx }));
    }
}

/// A move button crossed the 500 ms hold threshold (battle only — the lobby
/// long-press goes through wasm_lobby_long_press). On the web the hold
/// LATCHES: the pointer-up release is swallowed (see [`hold_end`]) and the
/// button stays held until clicked again or an option is committed.
#[wasm_bindgen] pub fn hold_move(player: u8, slot: u8) {
    if unlatch_if_held(player, false, slot) {
        return;
    }
    latch_held(player, false, slot);
    push_battle_input(BattleInput::Pad(PadEvent::HoldMove { player, slot }));
}

/// A party button crossed the 500 ms hold threshold.
#[wasm_bindgen] pub fn hold_switch(player: u8, idx: u8) {
    if unlatch_if_held(player, true, idx) {
        return;
    }
    latch_held(player, true, idx);
    push_battle_input(BattleInput::Pad(PadEvent::HoldSwitch { player, idx }));
}

/// The held button was released. Swallowed while a sticky latch is active —
/// on the web, letting go of the mouse doesn't end a hold.
#[wasm_bindgen] pub fn hold_end(player: u8) {
    if any_latched(player) {
        return;
    }
    push_battle_input(BattleInput::Pad(PadEvent::HoldEnd { player }));
}

fn enter_demo_mode() {
    DEMO_MODE.with(|d| *d.borrow_mut() = true);
    NEXT_GAME_AI.with(|n| *n.borrow_mut() = Some([true, true]));
    push_button(ButtonEvent::AiPreset);
}

#[wasm_bindgen] pub fn wasm_enter_demo_mode() {
    if !LOBBY_MODE.with(|m| *m.borrow()) { return; }
    enter_demo_mode();
}

#[wasm_bindgen] pub fn wasm_reset() {
    if let Some(win) = web_sys::window() {
        win.location().reload().ok();
    }
}

#[wasm_bindgen] pub fn wasm_toggle_ai_pause() -> bool {
    let new_state = AI_PAUSED.with(|p| { let v = !*p.borrow(); *p.borrow_mut() = v; v });
    new_state
}

#[wasm_bindgen] pub fn wasm_enter_vs_ai_mode() {
    if !LOBBY_MODE.with(|m| *m.borrow()) { return; }
    // p1=AI (White), p2=human (Red): p2 still picks their controls.
    NEXT_GAME_AI.with(|n| *n.borrow_mut() = Some([true, false]));
    push_button(ButtonEvent::AiPreset);
}

#[wasm_bindgen] pub fn is_lobby_mode() -> bool {
    LOBBY_MODE.with(|m| *m.borrow())
}

/// Long-press lobby handler: `player` pressed long → their opponent becomes
/// AI-controlled (ready) and the presser proceeds to the controls picker.
#[wasm_bindgen] pub fn wasm_lobby_long_press(player: u8) {
    if !LOBBY_MODE.with(|m| *m.borrow()) { return; }
    push_button(ButtonEvent::LongPress { player });
}

#[wasm_bindgen] pub fn submit_text(line: String) {
    let cmd = line.trim();

    // Global commands always available
    match cmd {
        ":reset" | ":restart" => { wasm_reset(); return; }
        ":anim off" => { ANIM_ENABLED.with(|a| *a.borrow_mut() = false); print_log("[anim] animations OFF"); return; }
        ":anim on"  => { ANIM_ENABLED.with(|a| *a.borrow_mut() = true);  print_log("[anim] animations ON");  return; }
        "?" | ":help" | ":h" => { print_help(); return; }
        ":screens" | ":screen" => {
            let s = screen_states();
            print_log(&format!("[screen] p1 {} | p2 {} | view {}", s[0], s[1], s[2]));
            return;
        }
        _ => {}
    }

    if LOBBY_MODE.with(|m| *m.borrow()) {
        match cmd {
            ":ready ai" | ":vs ai" | ":red vs ai" | ":blue vs ai" => {
                // VS AI: P1=AI (White), P2=human (Red) — P2 still picks controls.
                NEXT_GAME_AI.with(|n| *n.borrow_mut() = Some([true, false]));
                push_button(ButtonEvent::AiPreset);
            }
            ":demo" => { enter_demo_mode(); }
            // Ready commands skip the picker: current highlight (Normal by
            // default; `p1 concealed` first to change it).
            ":ready" | ":ready both" => {
                push_button(ButtonEvent::Line(String::from("p1 ok")));
                push_button(ButtonEvent::Line(String::from("p2 ok")));
            }
            ":ready p1" => push_button(ButtonEvent::Line(String::from("p1 ok"))),
            ":ready p2" => push_button(ButtonEvent::Line(String::from("p2 ok"))),
            // Anything else goes to the ready sequence: picker grammar
            // (pN normal|concealed|ok) and :press/:hold/:release sims.
            other => push_button(ButtonEvent::Line(String::from(other))),
        }
        return;
    }

    // In-game: the line goes to the shared collector — identical grammar and
    // feedback to the firmware's USB CLI ("p1 2", "p2 s3", bare when only one
    // player is choosing; typing for a committed player unreadies them).
    push_battle_input(BattleInput::Line(String::from(cmd)));
}

#[wasm_bindgen] pub fn get_p1_pixels() -> Vec<u8> {
    P1_PIXELS.with(|p| p.borrow().clone())
}

#[wasm_bindgen] pub fn get_p2_pixels() -> Vec<u8> {
    P2_PIXELS.with(|p| p.borrow().clone())
}

#[wasm_bindgen] pub fn get_led_state() -> Vec<u32> {
    if LOBBY_MODE.with(|m| *m.borrow()) {
        return lobby_led_frame().to_vec();
    }
    LED_STATE.with(|l| l.borrow().to_vec())
}

#[wasm_bindgen] pub fn get_flash_state() -> Vec<u8> {
    FLASH.with(|f| {
        let state = f.borrow().to_vec();
        *f.borrow_mut() = [0, 0];
        state
    })
}

// ── Entry point ───────────────────────────────────────────────────────────────

#[wasm_bindgen(start)]
pub fn start() {
    console_error_panic_hook::set_once();
    spawn_local(run_game_loop());
}

// ── OLED helpers ──────────────────────────────────────────────────────────────

fn draw_lobby_screen(player: u8, ready: bool, ai: bool) {
    oled_apply(OledCmd::LobbyState { player, ready, ai });
}

fn set_lobby_displays() {
    draw_lobby_screen(1, false, false);
    draw_lobby_screen(2, false, false);
    // LEDs driven by lobby_led_frame() while LOBBY_MODE is active
}

// ── Game loop ─────────────────────────────────────────────────────────────────

/// Which engine the menu's game choice selects. THE decision is core's
/// (`DeviceSession::ruleset`); this just reads it out.
pub(crate) fn menu_ruleset() -> Ruleset {
    SESSION.with(|s| s.borrow().ruleset())
}

/// One Gen 3 battle: core drafts, constructs and drives it over the SAME
/// [`InputBus`] + [`ChoiceCollector`] pump the Gen 1 path uses. This function
/// is the seed, the wiring, and a team-list line on the console — there is no
/// Gen 3 input code on this platform at all, which is the point: the first
/// cut had its own pad feed and its own turn loop, and every collector
/// behaviour it skipped (stale-press flushing, B-to-unready, validation, the
/// AI think delay) came back as a bug.
async fn run_gen3_web_battle(
    seed: u64,
    six: bool,
    bus: &InputBus,
    modes: [ControlMode; 2],
    effects: &mut WebBattleEffects<'_>,
) {
    let Some(mut battle) = mega_blastoise_core::runner::gen3::drafted_battle(seed, six) else {
        print_log("Gen 3: could not draft teams.");
        return;
    };
    for (label, side) in [("White", &battle.sides[0]), ("Red", &battle.sides[1])] {
        let names: Vec<&str> = side.party.iter().map(|m| m.species.name).collect();
        print_log(&format!("{label}: {}", names.join(", ")));
    }
    mega_blastoise_core::runner::gen3::run_battle(
        &mut battle,
        bus,
        collect_battle_input(bus, seed, modes),
        effects,
    )
    .await;
}
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
