alex-berliner/mega_blastoise/gen3_battle/src/battle/mod.rs

//! A Gen 3 singles turn loop.
//!
//! Deliberately small. This resolves the parts of a turn that the arithmetic
//! core already knows how to answer: who moves first, what a hit takes off,
//! who faints, and when the battle is over. Abilities, held items and weather
//! are not here yet, and the module says so rather than pretending: see the
//! `Unsupported` note on [`Battle::step`].
//!
//! Nothing in here is shared with `gen1_battle`. A Gen 1 battle runs that
//! engine start to finish and never enters this module, which is what keeps
//! Gen 1 behaviour exactly as it was.

extern crate alloc;

use alloc::vec::Vec;

use crate::ability;
use crate::item;
use crate::data::{
    move_by_id, species_by_id, Boost, MoveEntry, SideCondition,
    SpeciesEntry, Status, Weather,
};
use crate::stats::{hp_stat, other_stat, Invest, Nature, Stat};
use crate::types::Type;

/// A tiny deterministic PRNG, so a battle can be replayed from its seed.
/// xorshift64*, which is plenty for damage rolls and crits.
#[derive(Clone, Copy, Debug)]
pub struct Rng(u64);

impl Rng {
    pub fn new(seed: u64) -> Self {
        // A zero state would stay zero forever.
        Rng(if seed == 0 { 0x9E3779B97F4A7C15 } else { seed })
    }

    pub fn next_u32(&mut self) -> u32 {
        let mut x = self.0;
        x ^= x >> 12;
        x ^= x << 25;
        x ^= x >> 27;
        self.0 = x;
        ((x.wrapping_mul(0x2545F4914F6CDD1D)) >> 32) as u32
    }

    /// Uniform in `0..n`.
    pub fn below(&mut self, n: u32) -> u32 {
        if n == 0 {
            0
        } else {
            self.next_u32() % n
        }
    }
}

/// One move on a mon, with its remaining PP.
#[derive(Clone, Copy, Debug)]
pub struct MoveSlot {
    pub entry: &'static MoveEntry,
    pub pp: u8,
    /// Set by the mon rather than the move. Only Hidden Power uses it, whose
    /// type in Gen 3 comes from the holder's IVs.
    pub typed_as: Option<Type>,
}
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
